mfolejewski/PiG_Pi4GPU/pictures/PCIe_X4_X16_ADP_4.png

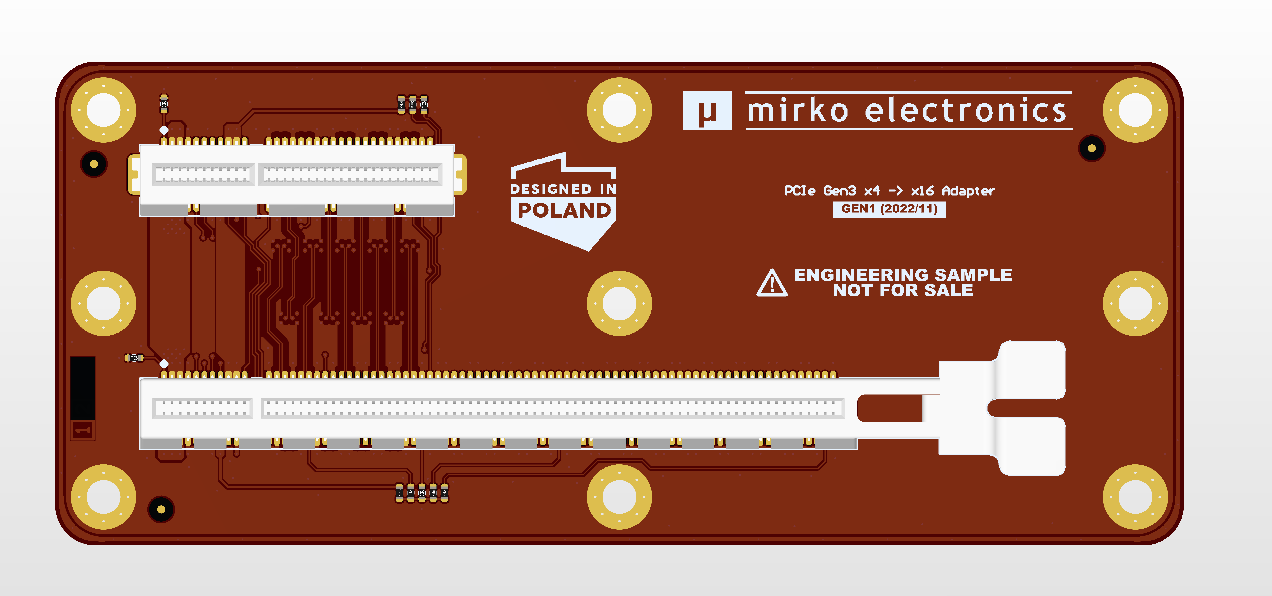
pictures/PCIe_X4_X16_ADP_4.png
