mfolejewski/PiG_Pi4GPU/pictures/Pi4GPU_2022-11-29_4.png

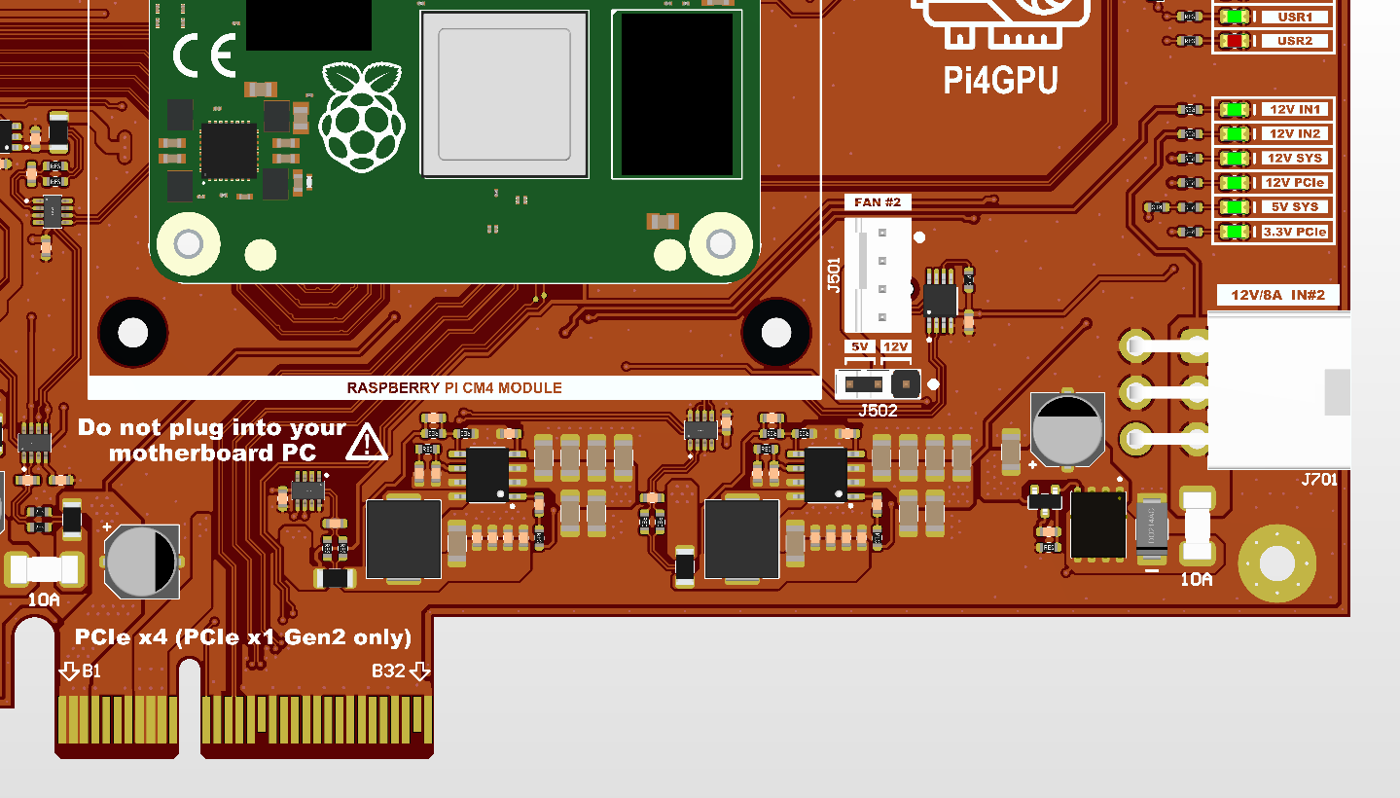
pictures/Pi4GPU_2022-11-29_4.png
