mfolejewski/PiG_Pi4GPU/pictures/Pi4GPU_2022-11-29_7.png

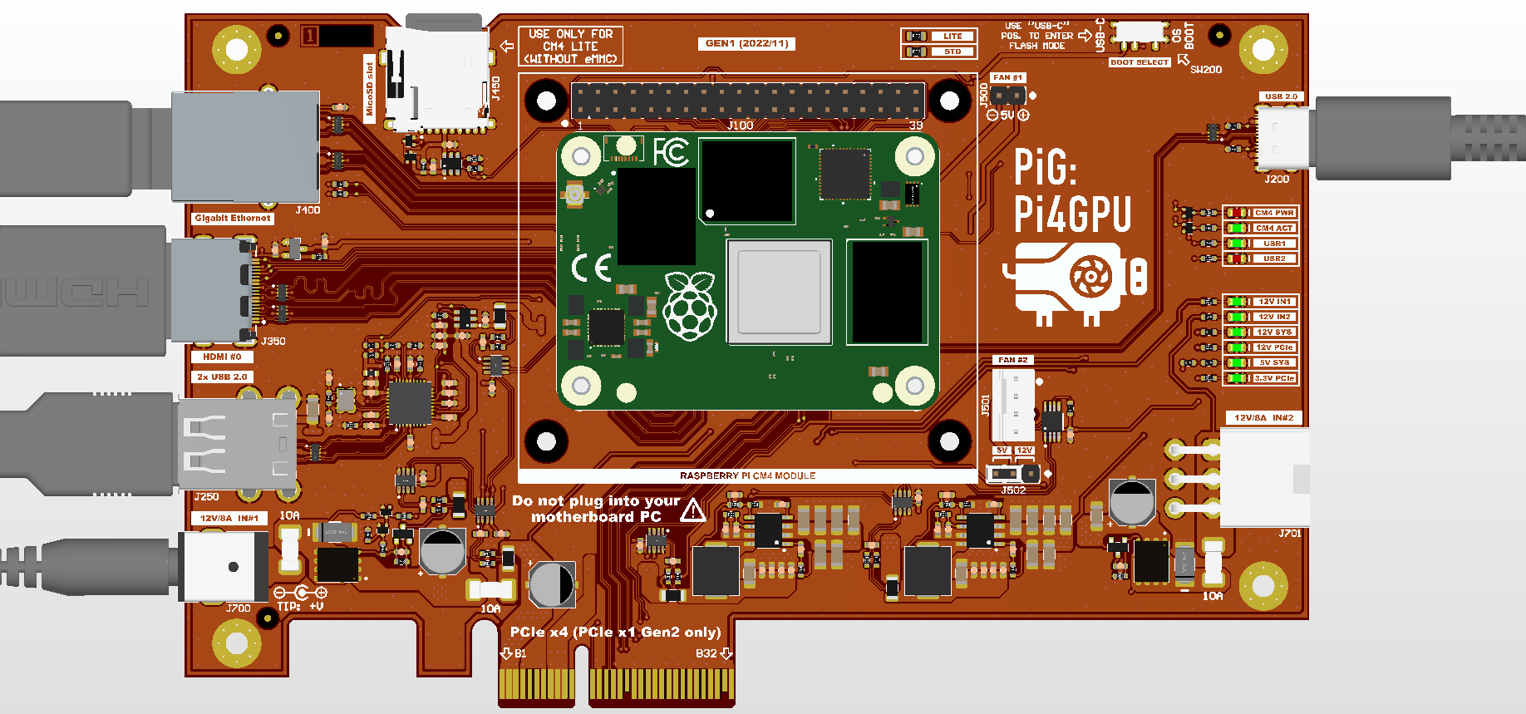
pictures/Pi4GPU_2022-11-29_7.png
