mfolejewski/PiG_Pi4GPU/pictures/Pi4GPU_v2_2023-04-13_6.png

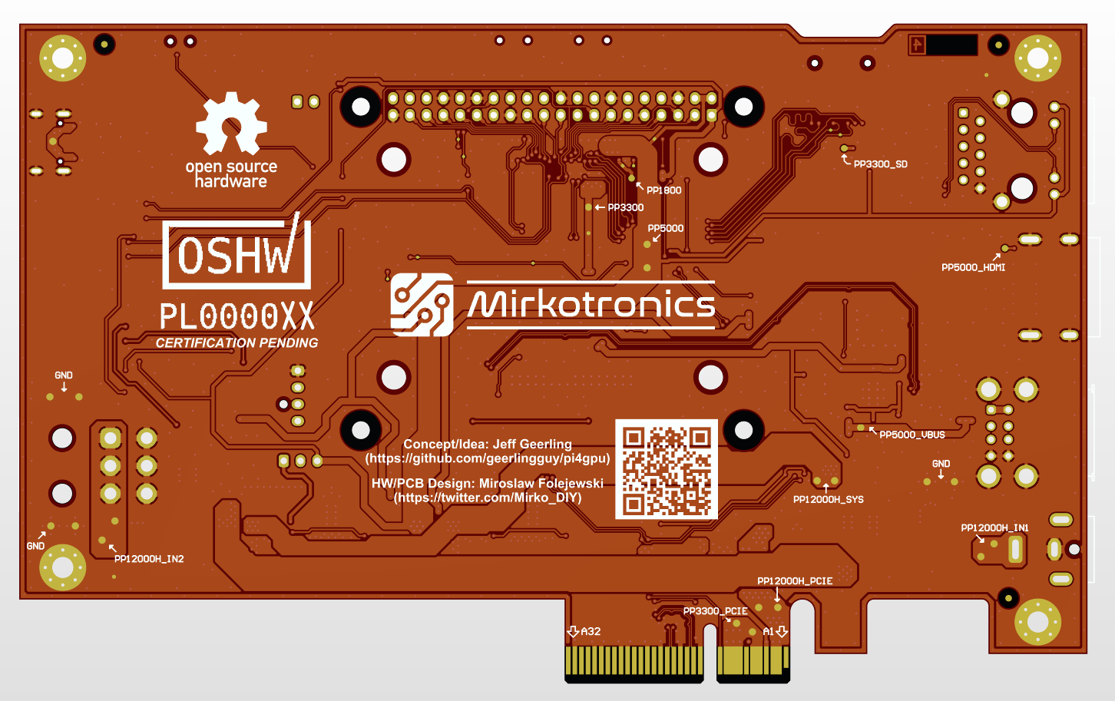
pictures/Pi4GPU_v2_2023-04-13_6.png
