mfolejewski/PiG_Pi4GPU/source_files/v2/pcb_stackup.png

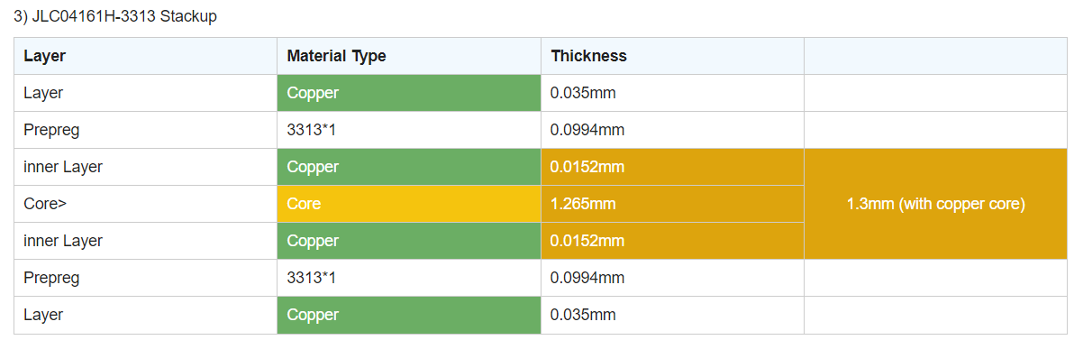
source_files/v2/pcb_stackup.png
